Sreyassss/BMS-BQ76920-Design-Low-side-switching-/bms 1.kicad_sch

## KiCad design bms 1.kicad_sch (2026-05-31)

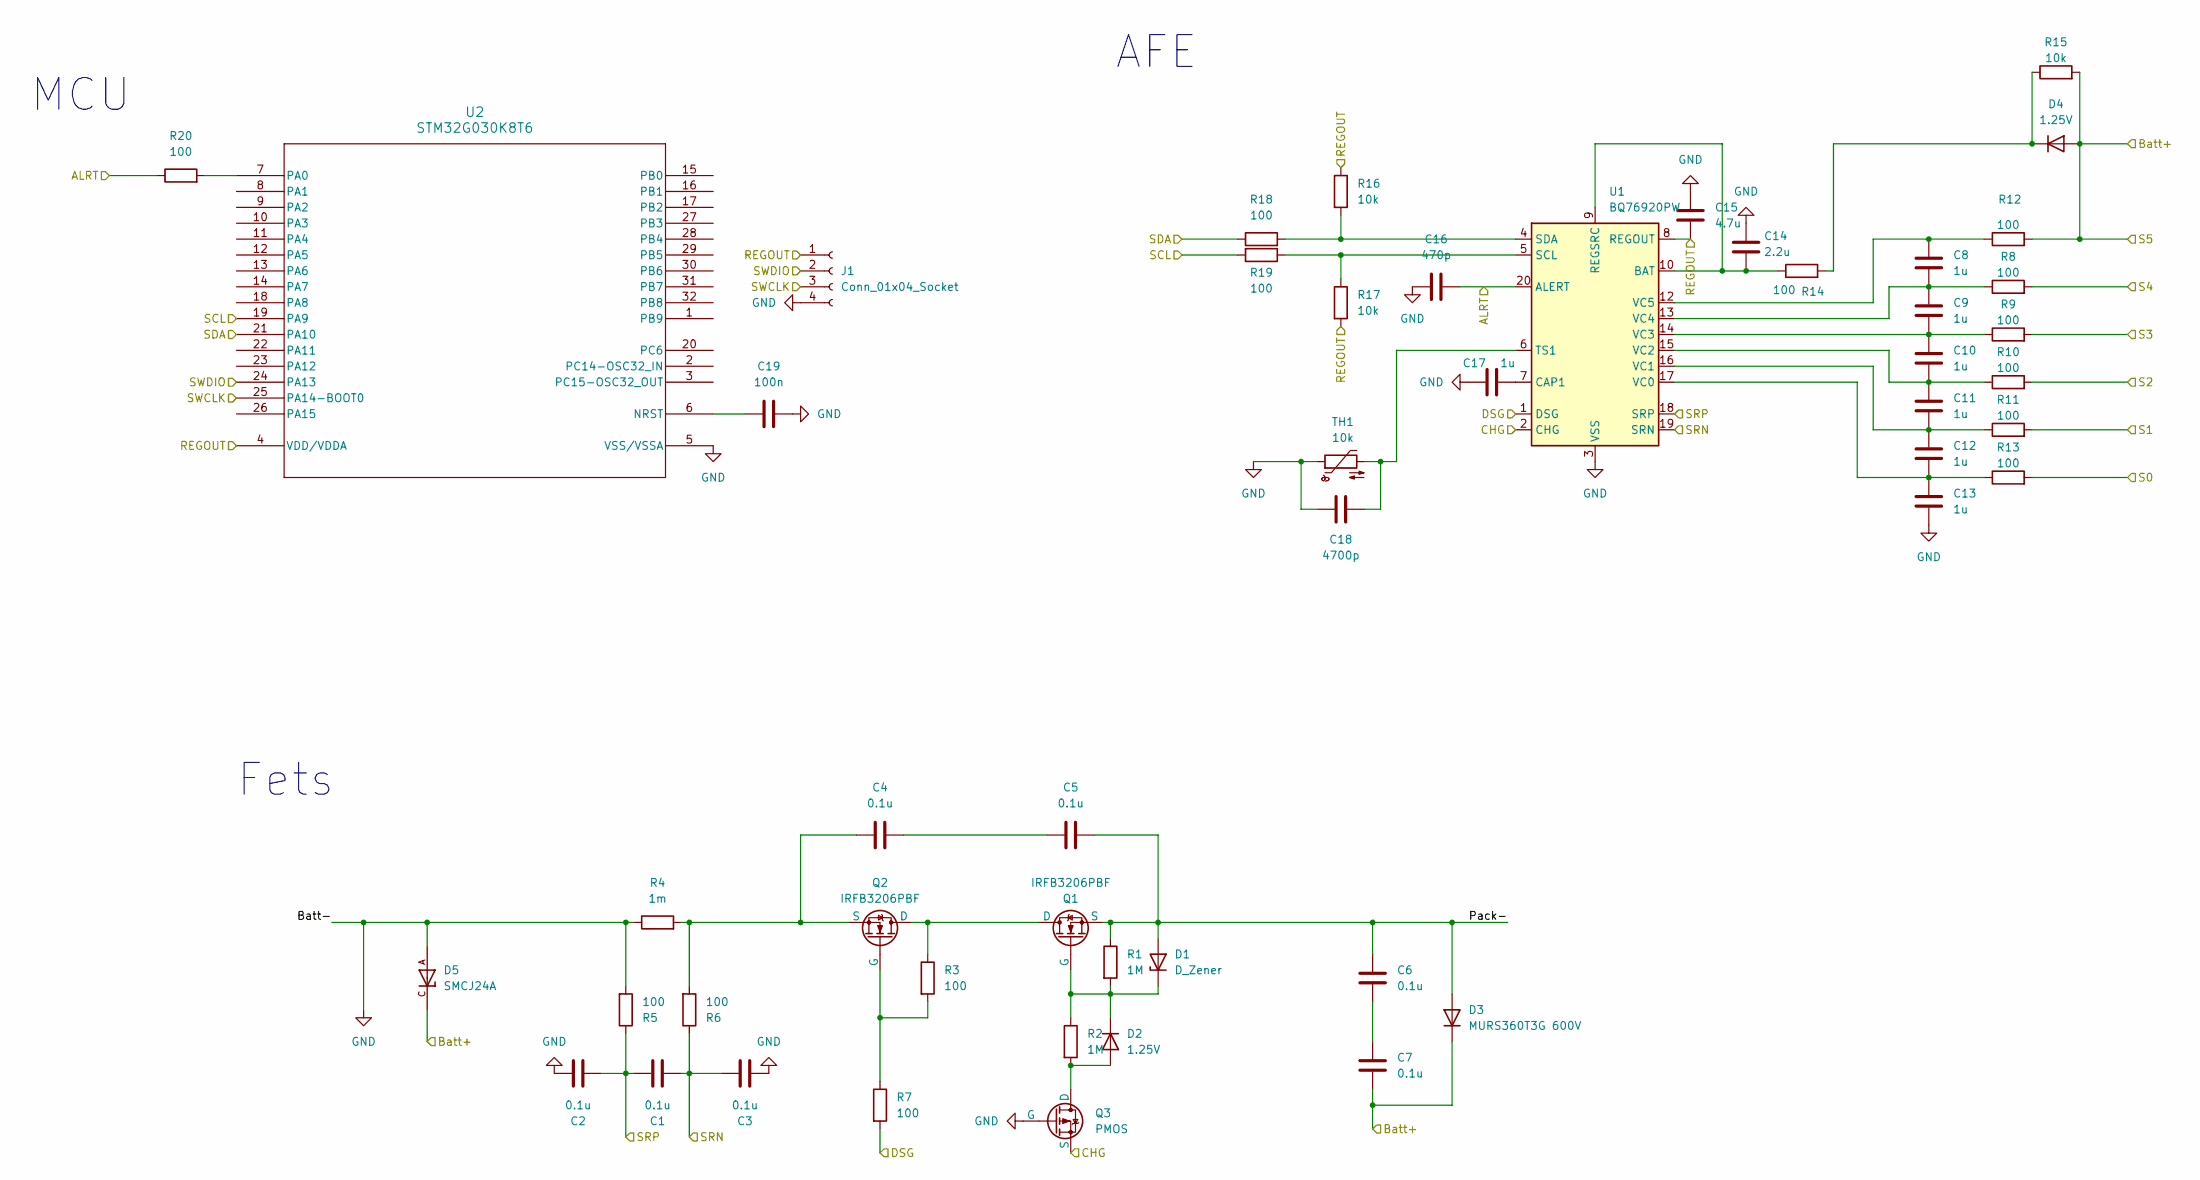
[picture p4: schematic bms 1.kicad_sch]

Parts:
C1, C2, C3, C4, C5, C6, C7: 0.1u
C8, C9, C10, C11, C12, C13, C17: 1u
C14: 2.2u
C15: 4.7u
C16: 470p
C18: 4700p
C19: 100n
D1: D_Zener
D2, D4: 1.25V
D3: MURS360T3G 600V
D5: SMCJ24A; DIOM7959X262N; PARTREV 11/20/15
J1: Conn_01x04_Socket
Q1, Q2: IRFB3206PBF
Q3: PMOS
R1, R2: 1M
R3, R5, R6, R7, R8, R9, R10, R11, R12, R13, R14, R18, R19, R20: 100
R4: 1m
R15, R16, R17: 10k
TH1: 10k
U1: BQ76920PW; TSSOP-20_4.4x6.5mm_P0.65mm
U2: STM32G030K8T6; LQFP-32

Connections:
ALRT: C16.2, R20.1, U1.20 (ALERT)
Batt+: C7.2, D3.1 (K), D4.2 (A), D5.C, R12.2, R15.2
CHG: Q3.3 (S), U1.2 (CHG)
DSG: R7.2, U1.1 (DSG)
GND: C2.1, C3.2, C13.2, C14.1, C15.1, C16.1, C17.1, C18.1, C19.2, D5.A, J1.4, Q3.2 (G), R4.1, R5.2, TH1.1, U1.3 (VSS), U2.5 (VSS/VSSA)
unnamed: C4.1, Q2.3 (S), R4.2, R6.2
unnamed: C4.2, C5.1
unnamed: C6.2, C7.1
unnamed: C8.1, R12.1, U1.12 (VC5)
unnamed: C8.2, C9.1, R8.1, U1.13 (VC4)
unnamed: C9.2, C10.1, R9.1, U1.14 (VC3)
unnamed: C10.2, C11.1, R10.1, U1.15 (VC2)
unnamed: C11.2, C12.1, R11.1, U1.16 (VC1)
unnamed: C12.2, C13.1, R13.1, U1.17 (VC0)
unnamed: C14.2, R14.1, U1.9 (REGSRC), U1.10 (BAT)
unnamed: C17.2, U1.7 (CAP1)
unnamed: C18.2, TH1.2, U1.6 (TS1)
unnamed: C19.1, U2.6 (NRST)
unnamed: D1.1 (K), D2.1 (K), Q1.2 (G), R1.2, R2.1
unnamed: D2.2 (A), Q3.1 (D), R2.2
unnamed: D4.1 (K), R14.2, R15.1
unnamed: Q1.1 (D), Q2.1 (D), R3.1
unnamed: Q2.2 (G), R3.2, R7.1
unnamed: R16.2, R18.2, U1.4 (SDA)
unnamed: R17.1, R19.1, U1.5 (SCL)
unnamed: R20.2, U2.7 (PA0)
Pack-: C5.2, C6.1, D1.2 (A), D3.2 (A), Q1.3 (S), R1.1
REGOUT: C15.2, J1.1, R16.1, R17.2, U1.8 (REGOUT), U2.4 (VDD/VDDA)
S0: R13.2
S1: R11.2
S2: R10.2
S3: R9.2
S4: R8.2
SCL: R19.2, U2.19 (PA9)
SDA: R18.1, U2.21 (PA10)
SRN: C1.2, C3.1, R6.1, U1.19 (SRN)
SRP: C1.1, C2.2, R5.1, U1.18 (SRP)
SWCLK: J1.3, U2.25 (PA14-BOOT0)
SWDIO: J1.2, U2.24 (PA13)

Notes on the sheet:
MCU
AFE
Fets
